shimotoriharuki/IGC-RTP/Circuit/sensor_circuit/robotrace_sensorV4_B.png

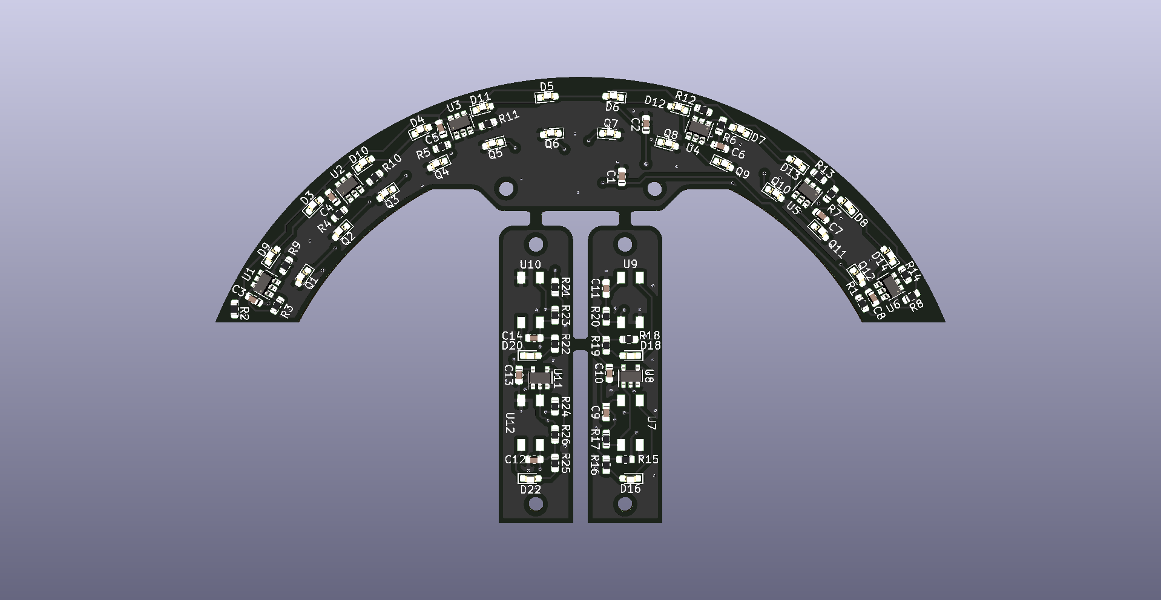
Circuit/sensor_circuit/robotrace_sensorV4_B.png
