shimotoriharuki/IGC-RTP/Core/Src/VelocityCtrl.c

/*
 * VelocityCtrl.c
 *
 *  Created on: 2023/01/28
 *      Author: Haruki SHIMOTORI
 */

#include "VelocityCtrl.h"

#define WHEEL_RADIUS 11.25 //[mm]
#define PI 3.1415926535
#define ENCODER_RESOLUTION 4096
#define REDUCTION_RATIO 0.35 //Gear reduction ratio 0.35
#define VELOCITY_PER_CNT (2 * PI * WHEEL_RADIUS * REDUCTION_RATIO / ENCODER_RESOLUTION) //[m/s per cnt]
#define DELTA_T 0.001

static uint8_t velocity_control_enable_flag;
static uint8_t i_clear_flag;

static float velocity_control_term;
static float target_velocity;

float mon_current_velocity, mon_diff;

void calculateVelocityControlFlip(void)
{
	float p, d;
	static float i;

#ifdef RYUKU
	float kp = 1500, ki = 5000, kd = 0.;
#elif defined(I7)
	//float kp = 2500, ki = 5000, kd = 0;
	float kp = 5200, ki = 60000, kd = 0.;
	//float kp = 5800, ki = 100000, kd = 0.;
#endif

	float diff = 0.;
	static float pre_diff = 0.;
	float current_velocity = getCurrentVelocity();

	if(velocity_control_enable_flag == 1){
		if(i_clear_flag == 1){
			i = 0;
			i_clear_flag = 0;
		}

		diff = target_velocity - current_velocity;
		//mon_diff = diff;
		p = kp * diff; //P制御
		i += ki * diff * DELTA_T; //I制御
		d = kd * (diff - pre_diff) / DELTA_T; //D制御

		//if(i >= 1000) i = 1000;
		//if(i <= -1000) i = -1000;

		velocity_control_term = p + i + d;

		pre_diff = diff;

	}

}

float getVelocityControlTerm(void)
{
	return velocity_control_term;
}

void setTargetVelocity(float velocity)
{
	target_velocity = velocity;
}

float getCurrentVelocity(void)
{
	int16_t enc_l = 0, enc_r = 0;
	getEncoderCnt(&enc_l, &enc_r);
	float enc_cnt = (enc_l + enc_r) / 2;

	float current_velocity = VELOCITY_PER_CNT * enc_cnt;
	mon_current_velocity = current_velocity;

	return current_velocity;
}

float getTargetVelocity()
{
	return target_velocity;
}

void startVelocityControl(void)
{
	velocity_control_enable_flag = 1;
	i_clear_flag = 1;
}

void stopVelocityControl(void)
{
	velocity_control_enable_flag = 0;
}

void setClearFlagOfVelocityControlI(void)
{
	i_clear_flag = 1;
}
