shimotoriharuki/IGC-RTP/Core/Inc/IMU.h

/*
 * IMU.h
 *
 *  Created on: 2023/02/11
 *      Author: ryuku
 */

#ifndef INC_IMU_H_
#define INC_IMU_H_

#include "MPU6500.h"
#include "math.h"

#define R_IMU 0.85 //0.03 Lowpath filter constant. The smaller it is, the more effective/


uint8_t initGyro();
void updateIMUValue();
float getOmega();
float getTheta10mm();
void clearTheta10mm();

#endif /* INC_IMU_H_ */
