shimotoriharuki/IGC-RTP/Core/Src/LED.c

/*
 * LED.c
 *
 *  Created on: 2023/02/12
 *      Author: Haruki SHIMOTORI
 */

#include "LED.h"

void setLED(uint8_t color)
{
	if(color == 'R'){
		HAL_GPIO_WritePin(GPIOC, GPIO_PIN_13, GPIO_PIN_RESET); //R
		HAL_GPIO_WritePin(GPIOC, GPIO_PIN_14, GPIO_PIN_SET); //G
		HAL_GPIO_WritePin(GPIOC, GPIO_PIN_15, GPIO_PIN_SET); //B
	}
	else if(color == 'G'){
		HAL_GPIO_WritePin(GPIOC, GPIO_PIN_13, GPIO_PIN_SET);
		HAL_GPIO_WritePin(GPIOC, GPIO_PIN_14, GPIO_PIN_RESET);
		HAL_GPIO_WritePin(GPIOC, GPIO_PIN_15, GPIO_PIN_SET);
	}
	else if(color == 'B'){
		HAL_GPIO_WritePin(GPIOC, GPIO_PIN_13, GPIO_PIN_SET);
		HAL_GPIO_WritePin(GPIOC, GPIO_PIN_14, GPIO_PIN_SET);
		HAL_GPIO_WritePin(GPIOC, GPIO_PIN_15, GPIO_PIN_RESET);
	}
	else if(color == 'M'){
		HAL_GPIO_WritePin(GPIOC, GPIO_PIN_13, GPIO_PIN_RESET);
		HAL_GPIO_WritePin(GPIOC, GPIO_PIN_14, GPIO_PIN_SET);
		HAL_GPIO_WritePin(GPIOC, GPIO_PIN_15, GPIO_PIN_RESET);
	}
	else if(color == 'Y'){
		HAL_GPIO_WritePin(GPIOC, GPIO_PIN_13, GPIO_PIN_RESET);
		HAL_GPIO_WritePin(GPIOC, GPIO_PIN_14, GPIO_PIN_RESET);
		HAL_GPIO_WritePin(GPIOC, GPIO_PIN_15, GPIO_PIN_SET);
	}
	else if(color == 'C'){
		HAL_GPIO_WritePin(GPIOC, GPIO_PIN_13, GPIO_PIN_SET);
		HAL_GPIO_WritePin(GPIOC, GPIO_PIN_14, GPIO_PIN_RESET);
		HAL_GPIO_WritePin(GPIOC, GPIO_PIN_15, GPIO_PIN_RESET);
	}
	else if(color == 'W'){
		HAL_GPIO_WritePin(GPIOC, GPIO_PIN_13, GPIO_PIN_RESET);
		HAL_GPIO_WritePin(GPIOC, GPIO_PIN_14, GPIO_PIN_RESET);
		HAL_GPIO_WritePin(GPIOC, GPIO_PIN_15, GPIO_PIN_RESET);
	}
	else if(color == 'N'){
		HAL_GPIO_WritePin(GPIOC, GPIO_PIN_13, GPIO_PIN_SET);
		HAL_GPIO_WritePin(GPIOC, GPIO_PIN_14, GPIO_PIN_SET);
		HAL_GPIO_WritePin(GPIOC, GPIO_PIN_15, GPIO_PIN_SET);
	}
	else{
		HAL_GPIO_WritePin(GPIOC, GPIO_PIN_13, GPIO_PIN_RESET);
		HAL_GPIO_WritePin(GPIOC, GPIO_PIN_14, GPIO_PIN_RESET);
		HAL_GPIO_WritePin(GPIOC, GPIO_PIN_15, GPIO_PIN_RESET);
	}
}

// Uppercase: lighting, lowercase: lights out
void setRGB(uint8_t rgb)
{
	if(rgb == 'R')	HAL_GPIO_WritePin(GPIOC, GPIO_PIN_13, GPIO_PIN_RESET);
	else if(rgb == 'G')	HAL_GPIO_WritePin(GPIOC, GPIO_PIN_14, GPIO_PIN_RESET);
	else if(rgb == 'B')	HAL_GPIO_WritePin(GPIOC, GPIO_PIN_15, GPIO_PIN_RESET);


	if(rgb == 'r')	HAL_GPIO_WritePin(GPIOC, GPIO_PIN_13, GPIO_PIN_SET);
	else if(rgb == 'g')	HAL_GPIO_WritePin(GPIOC, GPIO_PIN_14, GPIO_PIN_SET);
	else if(rgb == 'b')	HAL_GPIO_WritePin(GPIOC, GPIO_PIN_15, GPIO_PIN_SET);

}
