shimotoriharuki/IGC-RTP/Core/Inc/LED.h

/*
 * LED.h
 *
 *  Created on: 2023/02/12
 *      Author: Haruki SHIMOTORI
 */

#ifndef INC_LED_H_
#define INC_LED_H_

#include "stm32f4xx_hal.h"

void setLED(uint8_t);
void setRGB(uint8_t);


#endif /* INC_LED_H_ */
