shimotoriharuki/IGC-RTP/Core/Inc/Switch.h

/*
 * Switch.h
 *
 *  Created on: 2023/02/12
 *      Author: Haruki SHIMOTORI
 */

#ifndef INC_SWITCH_H_
#define INC_SWITCH_H_

#include "stm32f4xx_hal.h"
#include "stdbool.h"

bool getSwitchStatus(uint8_t);


#endif /* INC_SWITCH_H_ */
