shimotoriharuki/IGC-RTP/Core/Inc/UserSelection.h

/*
 * UserSelection.h
 *
 *  Created on: Jan 28, 2023
 *      Author: under
 */

#ifndef INC_USERSELECTION_H_
#define INC_USERSELECTION_H_

//#define RYUKU
#define I7

#endif /* INC_USERSELECTION_H_ */
